adafruit/Adafruit-GPIO-Expander-Bonnet-PCBs/assets/4132.jpg

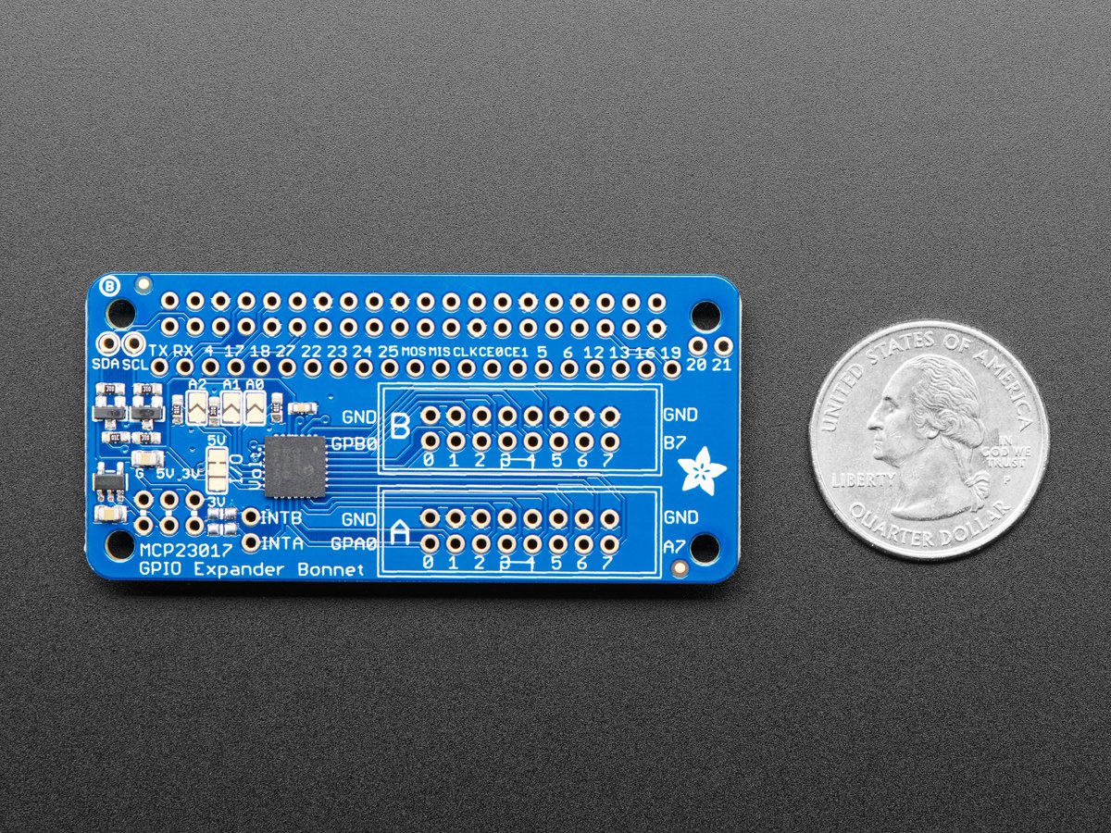
assets/4132.jpg
